kekiefer/riscbot/pcb/spektrum.asc

D1: LED
Q1: npn; 2N2222
R1: res; 270
R2: res; 100
R3: res; 10K
R4: res; 270
V1: voltage; 3.3; Rser=0
V2: voltage; PULSE(0 3.3 10000u 10n 10n 1000u 2000u 4)
Named nets: 0
.tran .05 startup
